AGHuhn/CDC_C4D/Hardware/Case/IMG_20210218_152949.jpg

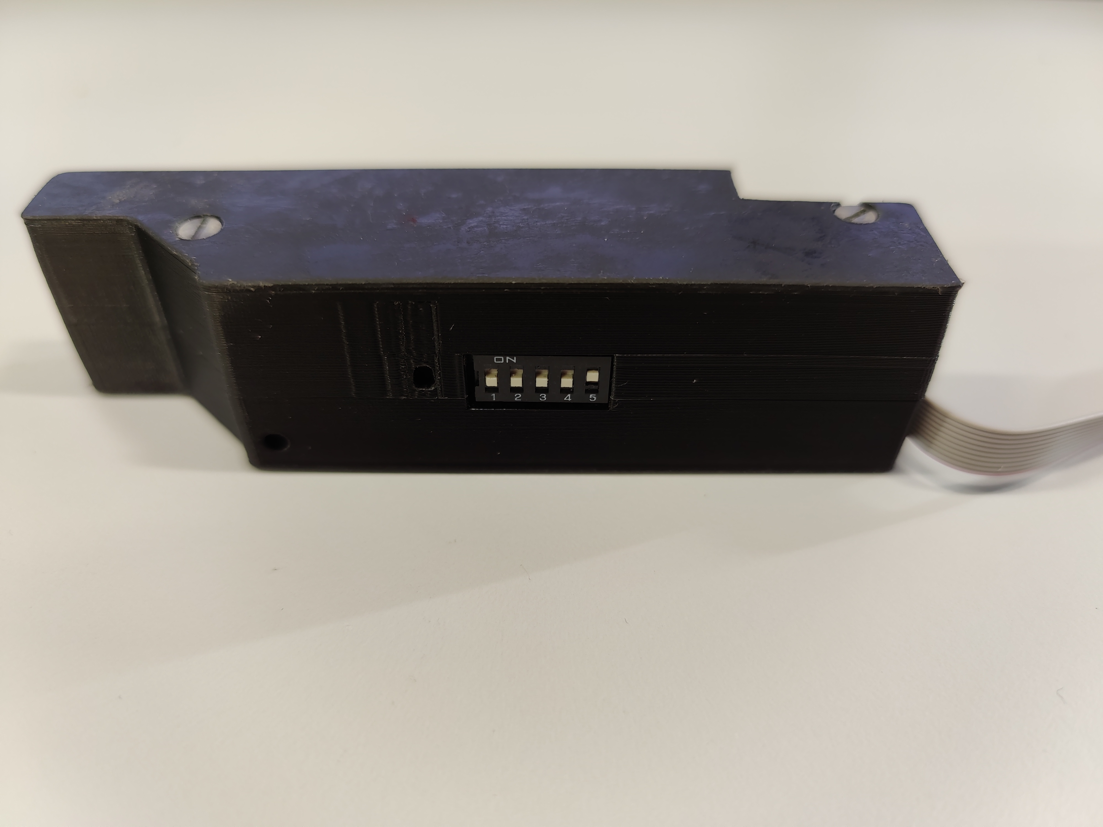
Hardware/Case/IMG_20210218_152949.jpg
