AGHuhn/CDC_C4D/Hardware/Case/IMG_20210218_153002.jpg

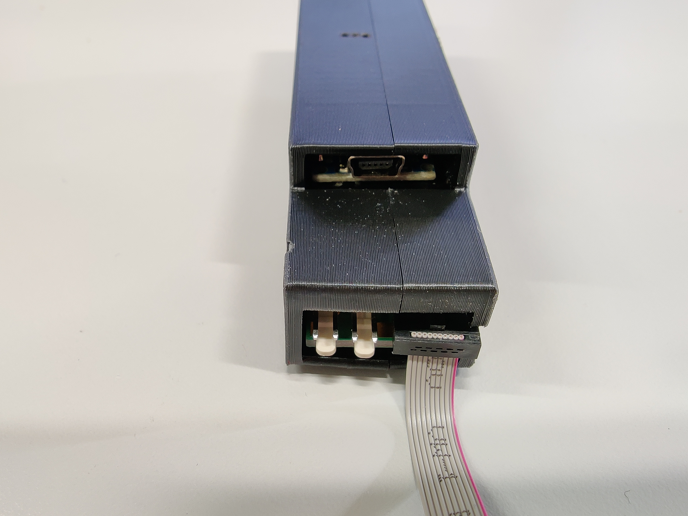
Hardware/Case/IMG_20210218_153002.jpg
