AGHuhn/CDC_C4D/Hardware/Detection_Head/scheme-detector_head.png

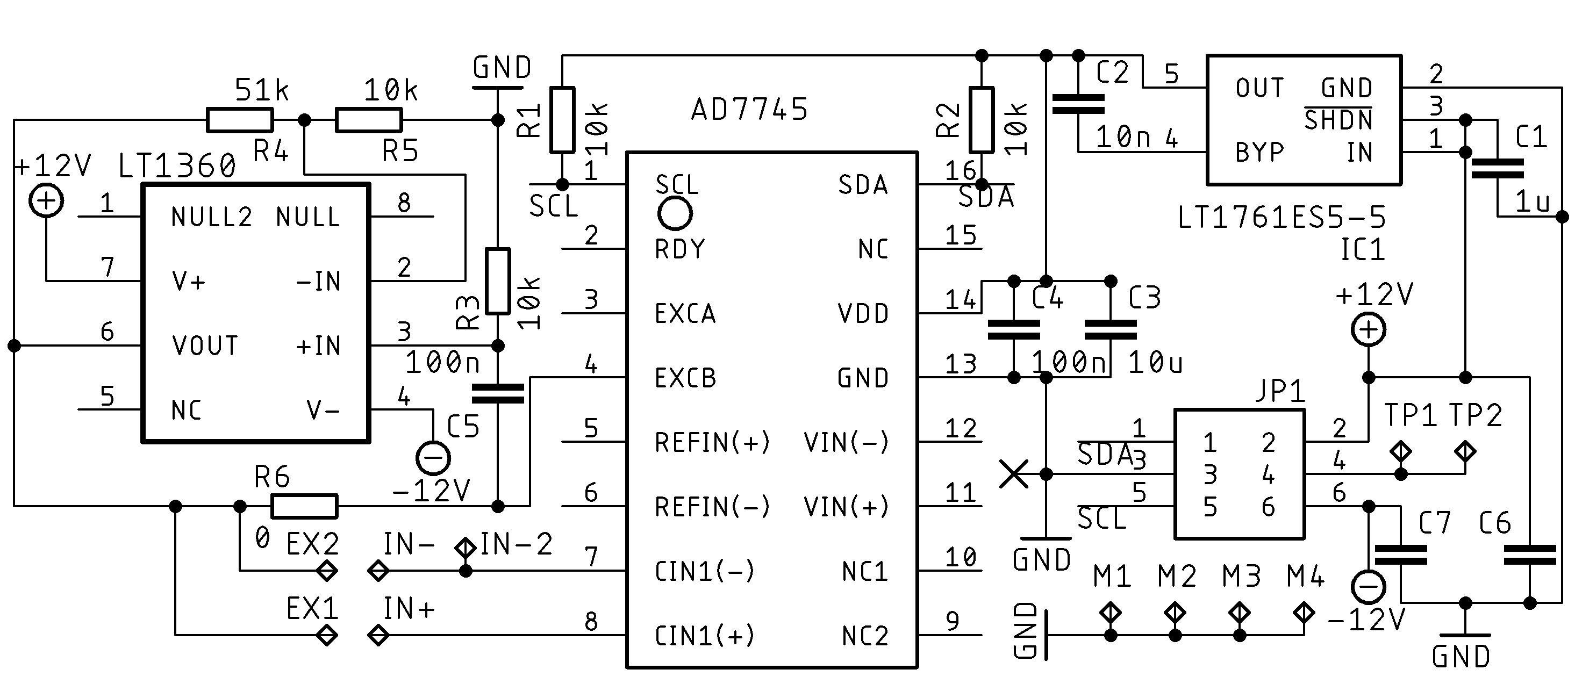
Hardware/Detection_Head/scheme-detector_head.png
