AGHuhn/CDC_C4D/Hardware/Supply_Unit/img/top.png

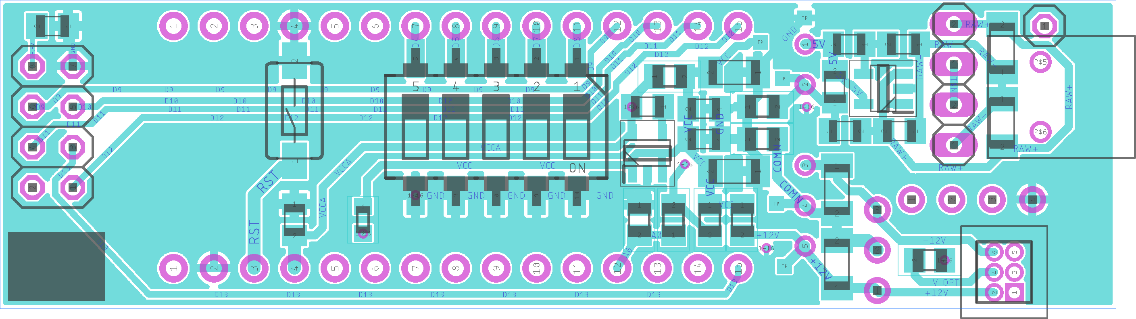
Hardware/Supply_Unit/img/top.png
