AGHuhn/CDC_C4D/Hardware/Supply_Unit/img/Top_nano_neu5.png

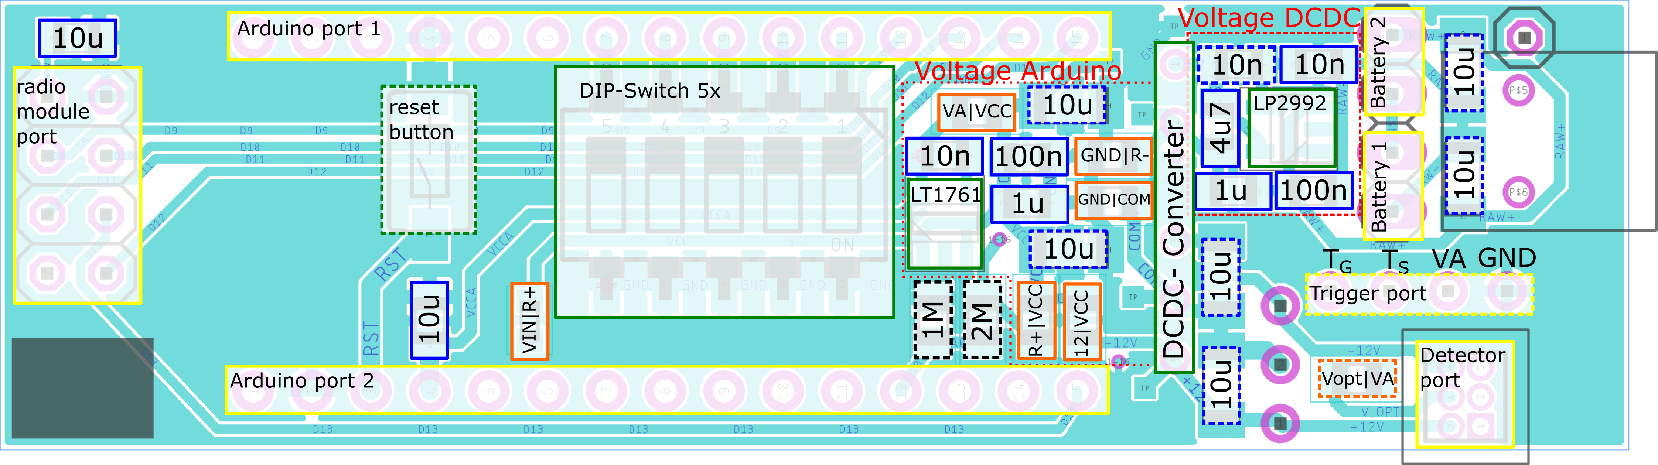
Hardware/Supply_Unit/img/Top_nano_neu5.png
