AGHuhn/CDC_C4D/Hardware/Supply_Unit/img/Top_nano_neu5_1_CN.png

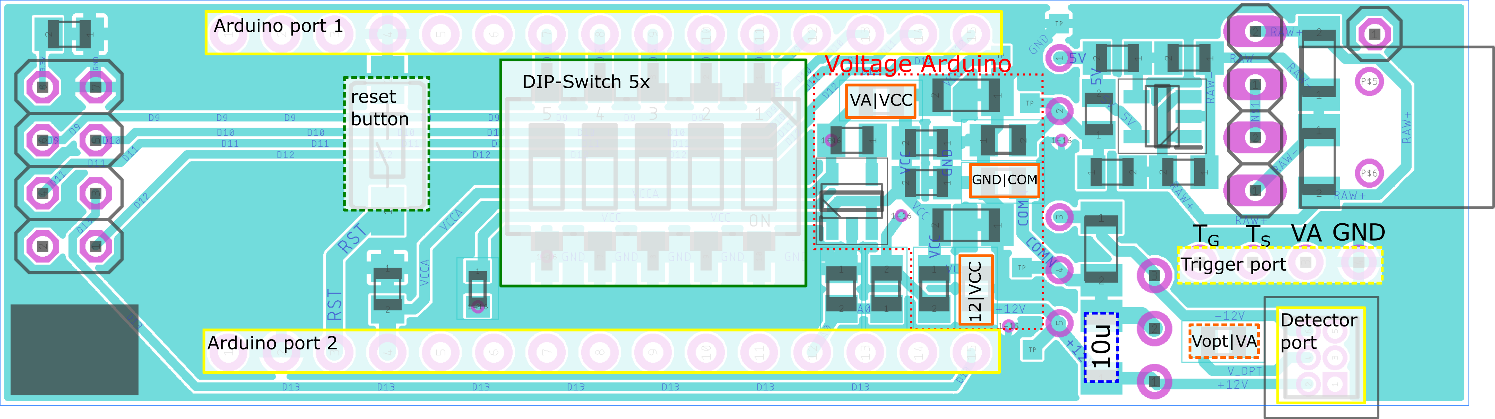
Hardware/Supply_Unit/img/Top_nano_neu5_1_CN.png
