AGHuhn/CDC_C4D/Hardware/Supply_Unit/img/Top_nano_neu5_3_RN.png

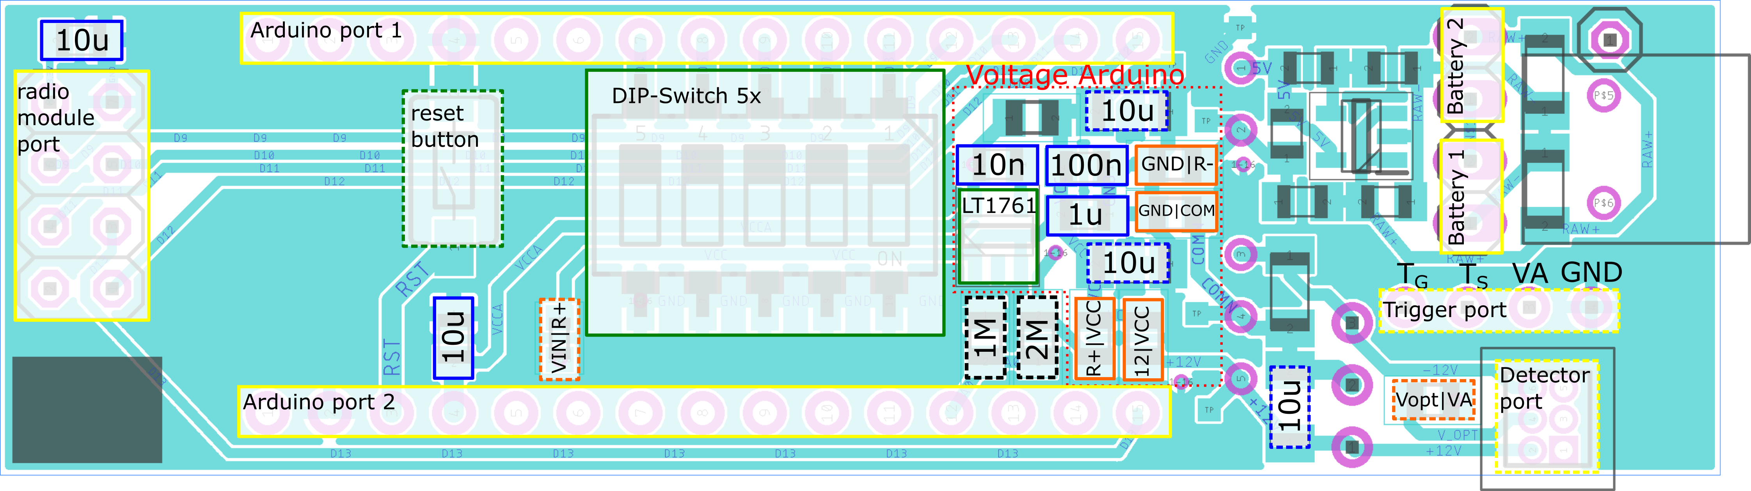
Hardware/Supply_Unit/img/Top_nano_neu5_3_RN.png
