AGHuhn/CDC_C4D/Hardware/Supply_Unit/img/Top_nano_neu5_4a.png

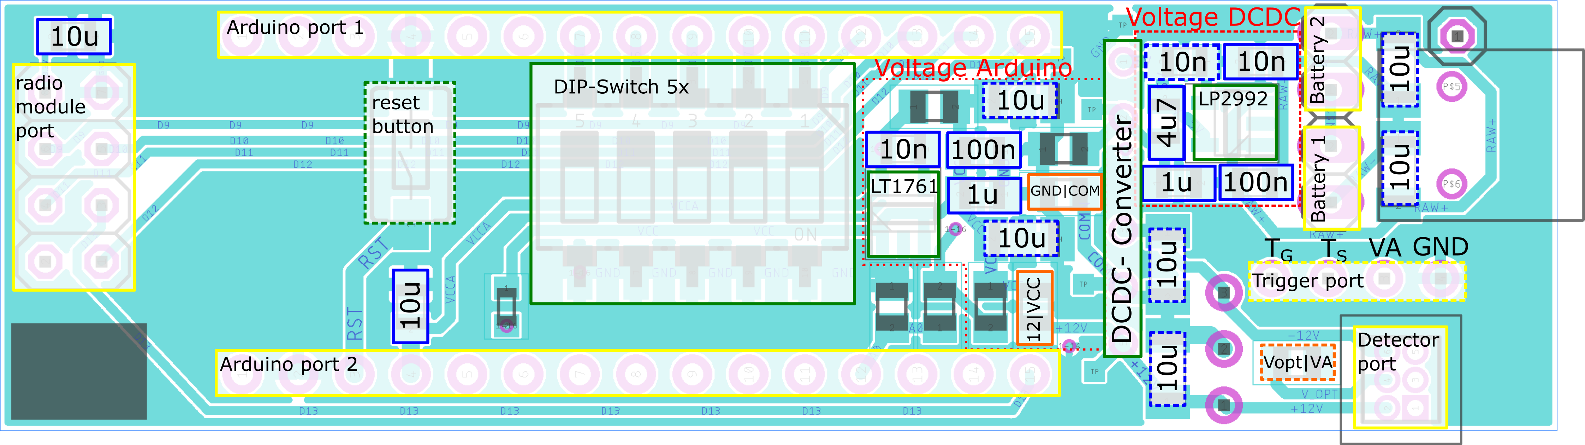
Hardware/Supply_Unit/img/Top_nano_neu5_4a.png
