AGHuhn/CDC_C4D/Hardware/Supply_Unit/img/Top_nano_neu5_4c.png

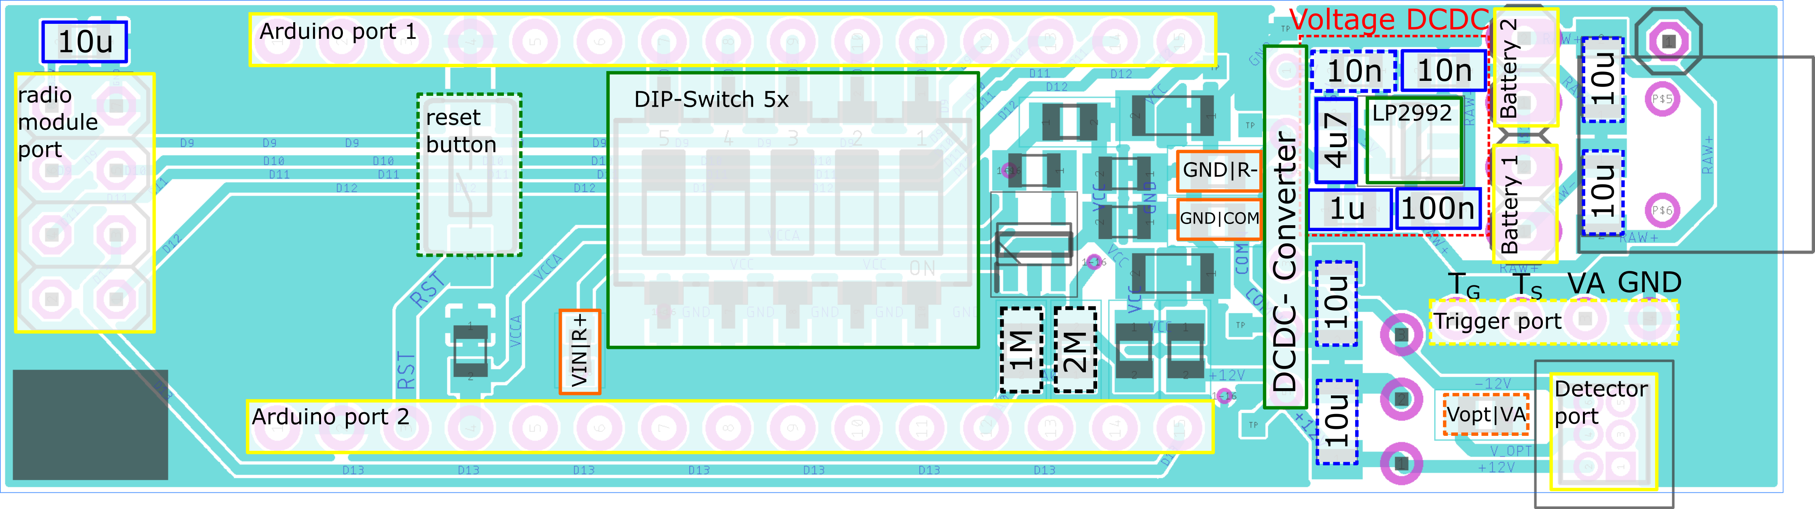
Hardware/Supply_Unit/img/Top_nano_neu5_4c.png
