AGHuhn/CDC_C4D/Hardware/Supply_Unit/scheme-supply_unit.png

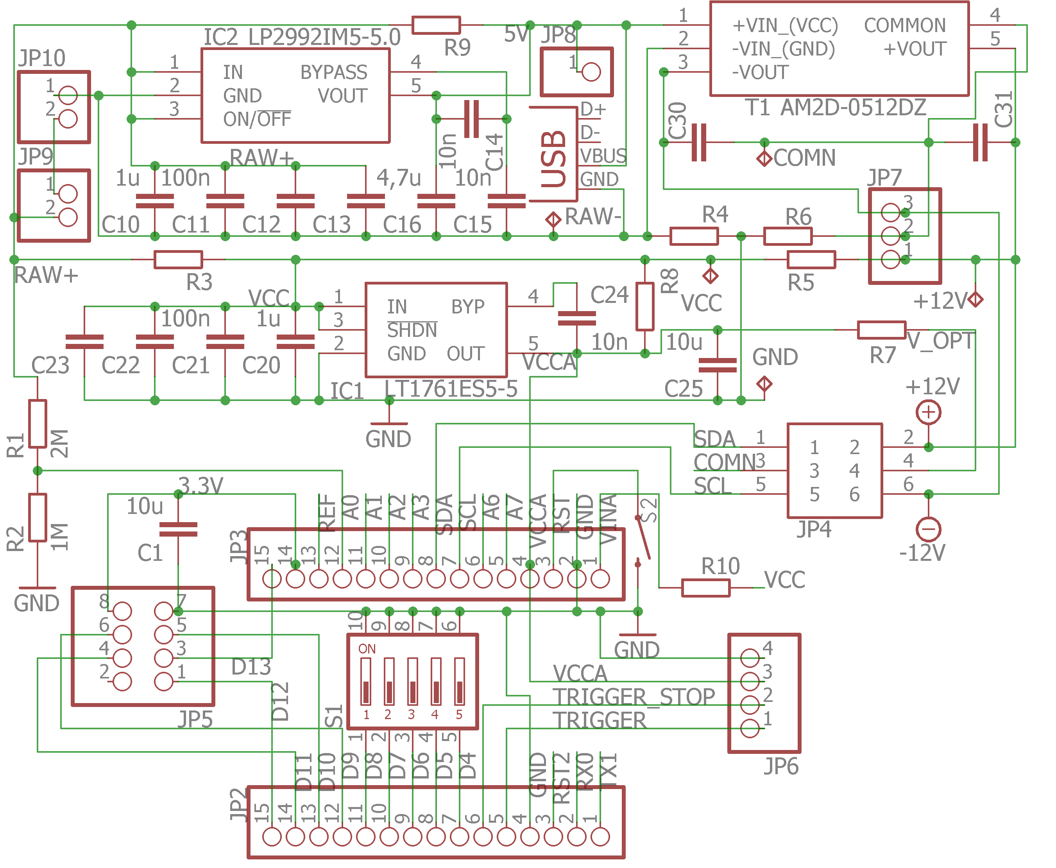
Hardware/Supply_Unit/scheme-supply_unit.png
