AGHuhn/CDC_C4D/Hardware/Trigger-Module/bottom.png

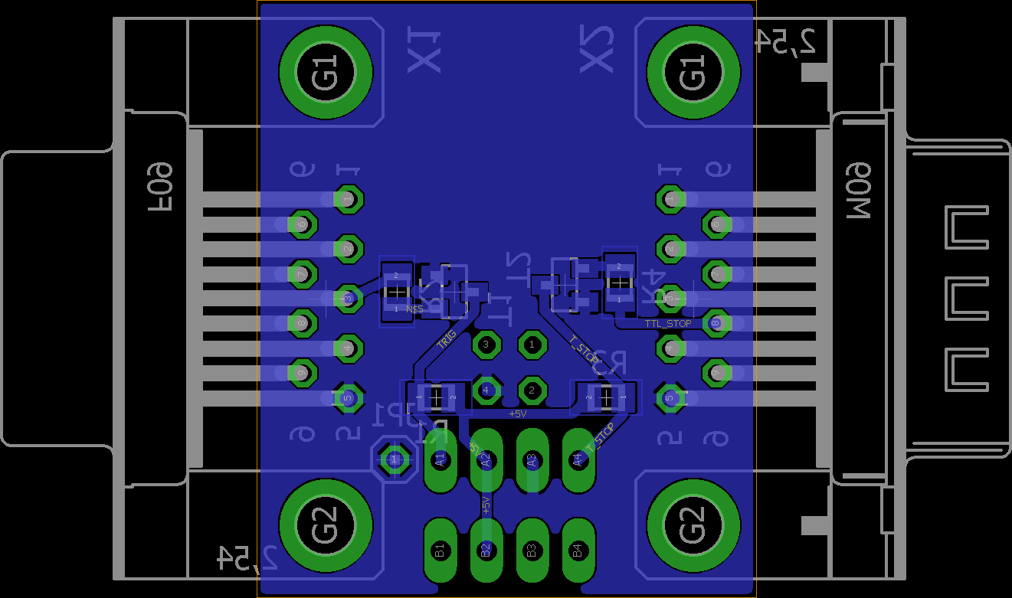
Hardware/Trigger-Module/bottom.png
