AGHuhn/CDC_C4D/Hardware/Trigger-Module/img_bottom.jpg

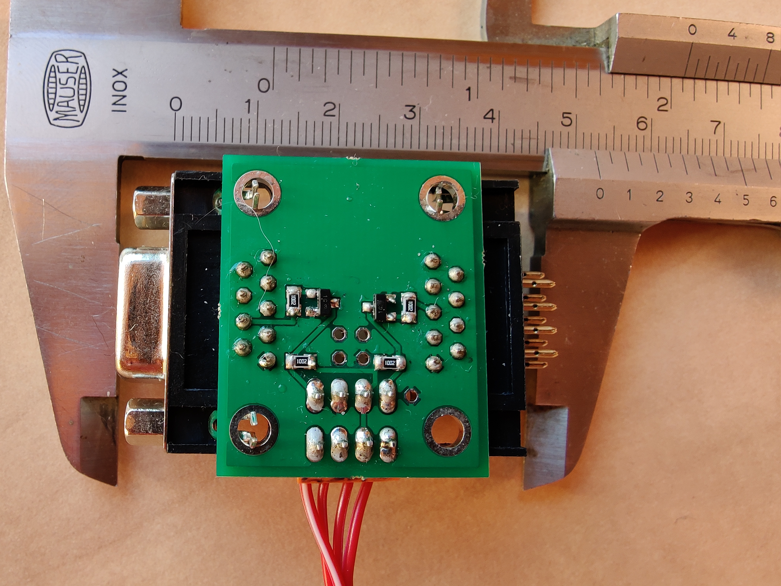
Hardware/Trigger-Module/img_bottom.jpg
