AGHuhn/CDC_C4D/Hardware/Trigger-Module/scheme_trigger-module.png

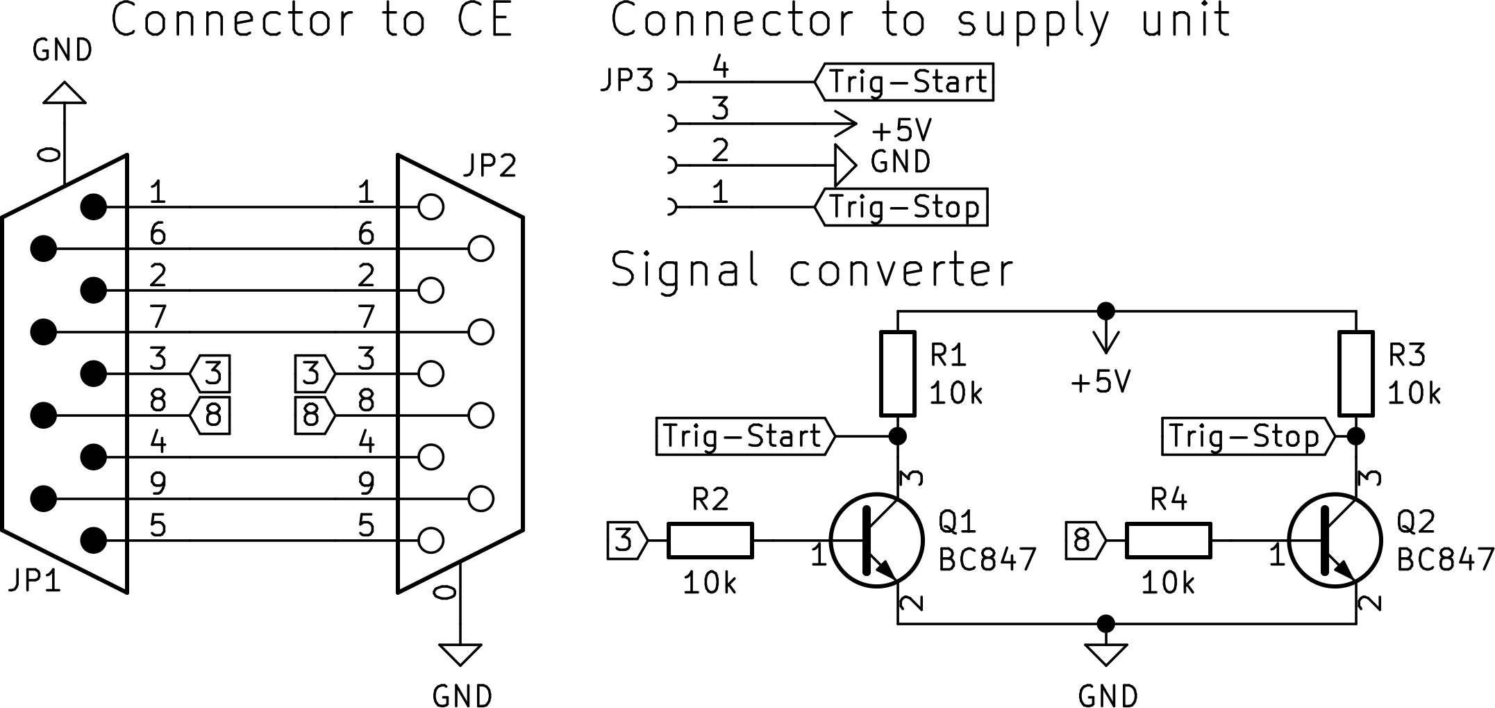
Hardware/Trigger-Module/scheme_trigger-module.png
