AGHuhn/CDC_C4D/Hardware/Trigger-Module/top.png

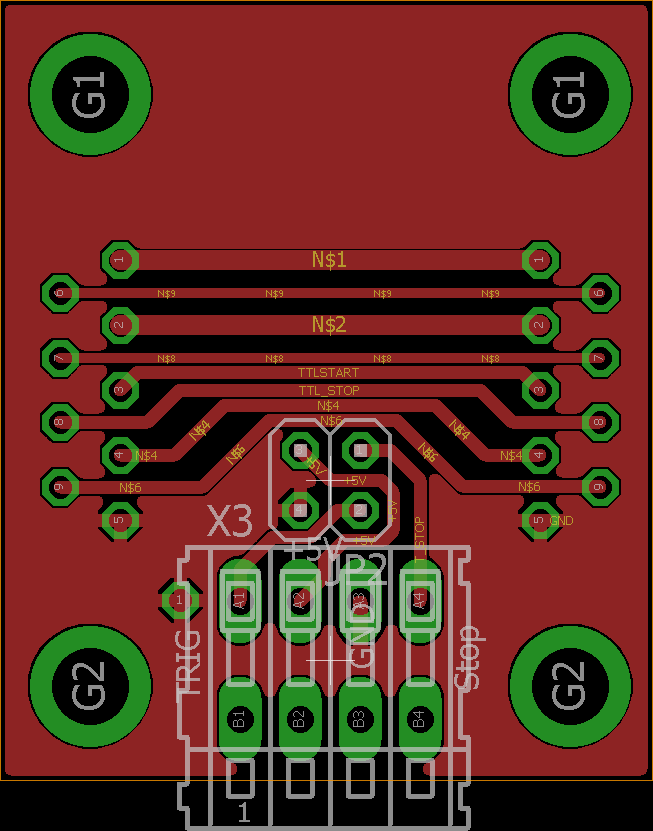
Hardware/Trigger-Module/top.png
